tinkode56/AirQM_ESP32C3/components/oled_display/include/oled_splash_screen.h

/*
 * @Author: calin.acr 
 * @Date: 2024-09-09 20:15:32 
 * @Last Modified by: calin.acr
 * @Last Modified time: 2024-09-09 21:28:15
 */

#if !defined(_OLED_SPLASH_SCREEN_H)
#define _OLED_SPLASH_SCREEN_H

// 'splash_screen', 128x64px
const char splash_screen[] = {
0x00, 0x00, 0x00, 0x00, 0x00, 0x00, 0x00, 0x00, 0x00, 0x00, 0x00, 0x00, 0x00, 0x00, 0xe0, 0xfc,  // 16
0xfc, 0xfc, 0xfc, 0xfc, 0xfc, 0xc0, 0x00, 0x00, 0x00, 0x00, 0x00, 0x00, 0xdc, 0xdc, 0xdc, 0xdc,  // 32
0x00, 0x00, 0x00, 0x00, 0xc0, 0xc0, 0xc0, 0x80, 0x80, 0xc0, 0xc0, 0x00, 0x00, 0xc0, 0xf0, 0xf0,  // 48
0xf8, 0xf8, 0x7c, 0x3c, 0x3c, 0x7c, 0xf8, 0xf8, 0xf8, 0xf0, 0xe0, 0x00, 0x00, 0x00, 0x00, 0xfc,  // 64
0xfc, 0xfc, 0xfc, 0xfc, 0xfc, 0xf0, 0x80, 0x00, 0x80, 0xf8, 0xfc, 0xfc, 0xfc, 0xfc, 0xfc, 0xfc,  // 80
0x00, 0x00, 0x00, 0x00, 0x00, 0x00, 0x00, 0x00, 0x00, 0x00, 0x80, 0xe0, 0xf0, 0xf8, 0xf8, 0xfc,  // 96
0x3c, 0x3c, 0x7c, 0xf8, 0xf8, 0xf8, 0xf0, 0xc0, 0x00, 0x00, 0xe0, 0xf0, 0xf8, 0xf8, 0x7c, 0x3c,  // 112
0x3c, 0xfc, 0xf8, 0xf8, 0xf0, 0xe0, 0x00, 0x00, 0x00, 0x00, 0x00, 0x00, 0x00, 0x00, 0x00, 0x00,  // 128
0x00, 0x00, 0x00, 0x00, 0x00, 0x00, 0x00, 0x00, 0x00, 0x00, 0x00, 0x80, 0xf0, 0xff, 0xff, 0x7f,  // 16
0x7b, 0x78, 0x7f, 0x7f, 0xff, 0xff, 0xfe, 0xf0, 0x80, 0x00, 0x00, 0x00, 0xff, 0xff, 0xff, 0xff,  // 32
0x00, 0x00, 0x00, 0x00, 0xff, 0xff, 0xff, 0xff, 0x0f, 0x07, 0x07, 0x00, 0x04, 0x7f, 0xff, 0xff,  // 48
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
0x81, 0x00, 0x3e, 0x7f, 0x7f, 0x3e, 0x1c, 0x00, 0x00, 0x00, 0x00, 0x00, 0x00, 0x00, 0x00, 0x00, // 
0x00, 0x00, 0x00, 0x00, 0x00, 0x00, 0x00, 0x00, 0x00, 0x00, 0x00, 0x00, 0x00, 0x00, 0x00, 0x00, // 
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
};


#endif // _OLED_SPLASH_SCREEN_H
